StelaVillagomez/funbio-grupo-5/Documentacion/Talleres en clase/Taller 8/Carla Ulloa.pdf

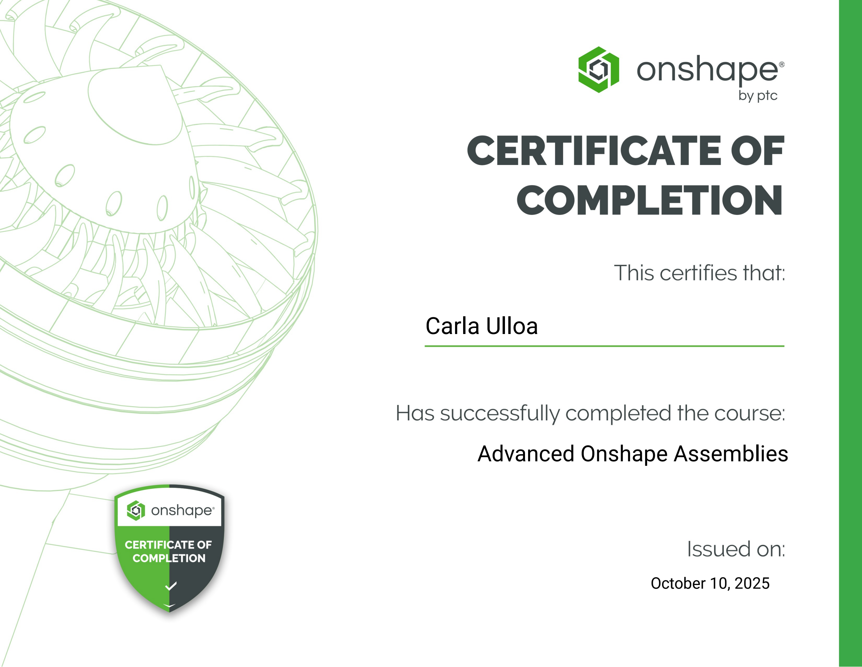
[picture p14: page 1]

Carla Ulloa

Advanced Onshape Assemblies

October 10, 2025
