StelaVillagomez/funbio-grupo-5/Documentacion/Talleres en clase/Taller 8/Luciana Vega.pdf

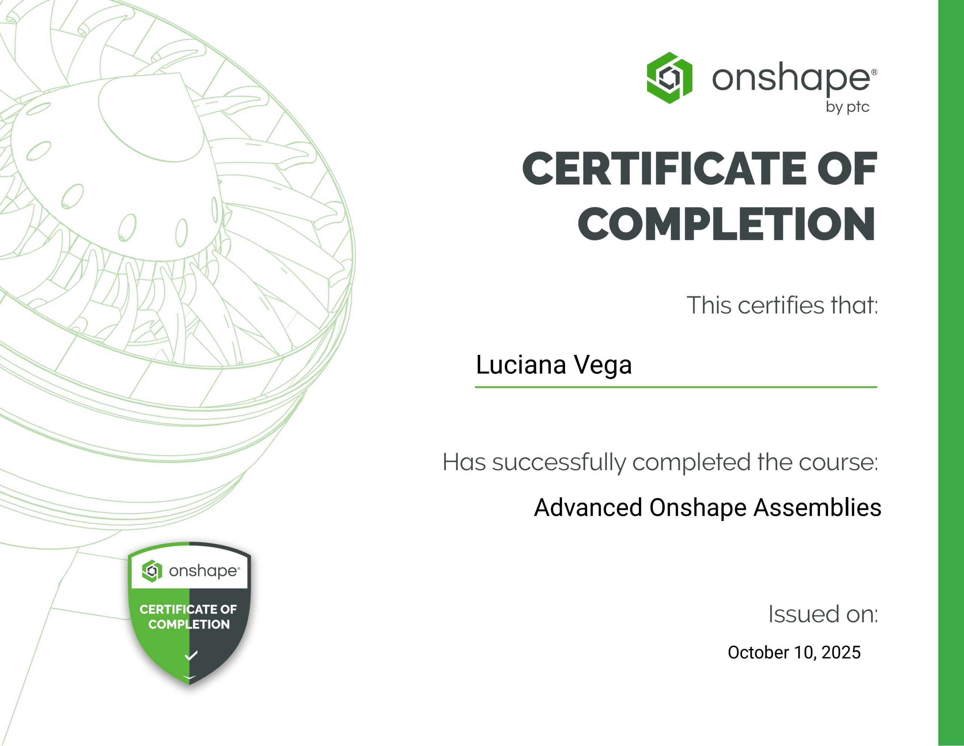
[picture p15: page 1]

Luciana Vega

Advanced Onshape Assemblies

October 10, 2025
