StelaVillagomez/funbio-grupo-5/Documentacion/Talleres en clase/Taller 8/Nahir Valladares.pdf

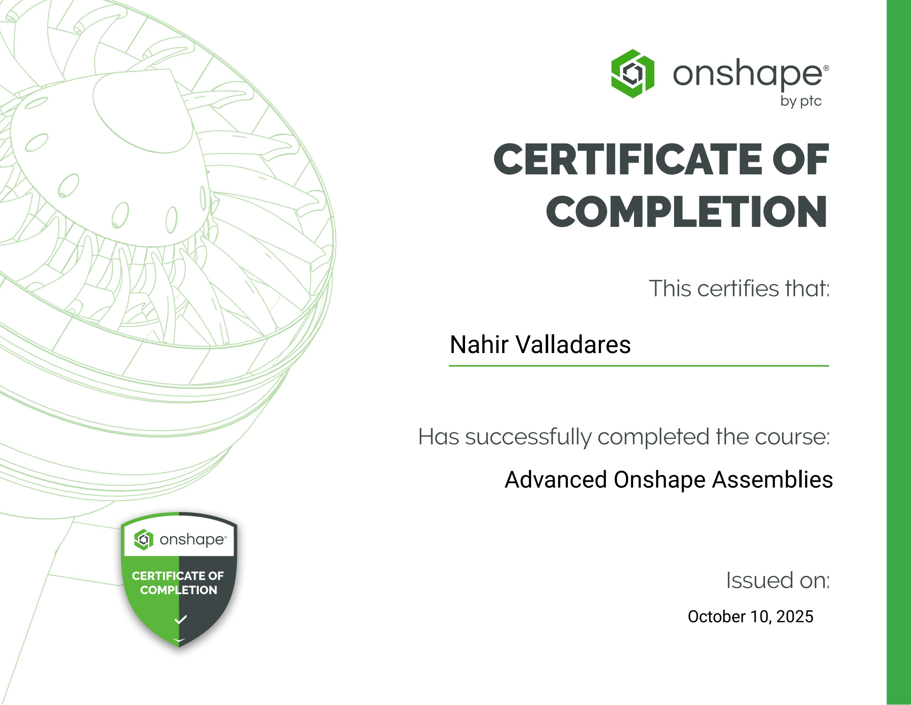
[picture p16: page 1]

Nahir Valladares

Advanced Onshape Assemblies

October 10, 2025
