StelaVillagomez/funbio-grupo-5/Documentacion/Talleres en clase/Taller 8/stela-villagomez.pdf

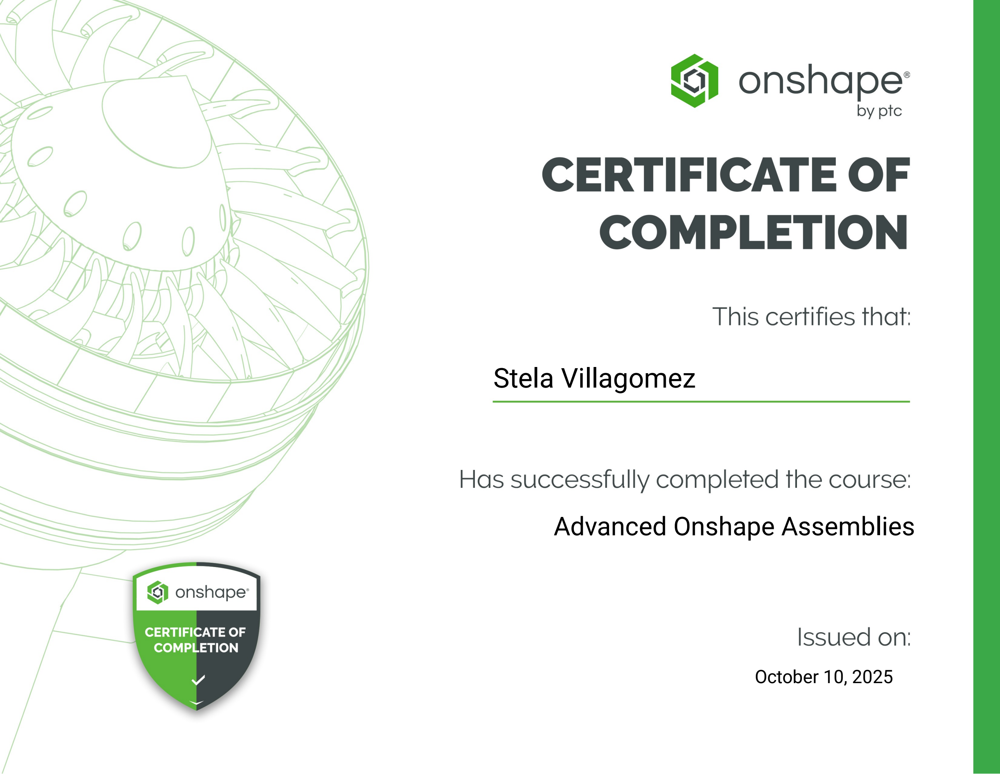
[picture p17: page 1]

Stela Villagomez

Advanced Onshape Assemblies

October 10, 2025
