StelaVillagomez/funbio-grupo-5/Documentacion/Talleres en clase/Taller 8/Carla Victoria.pdf

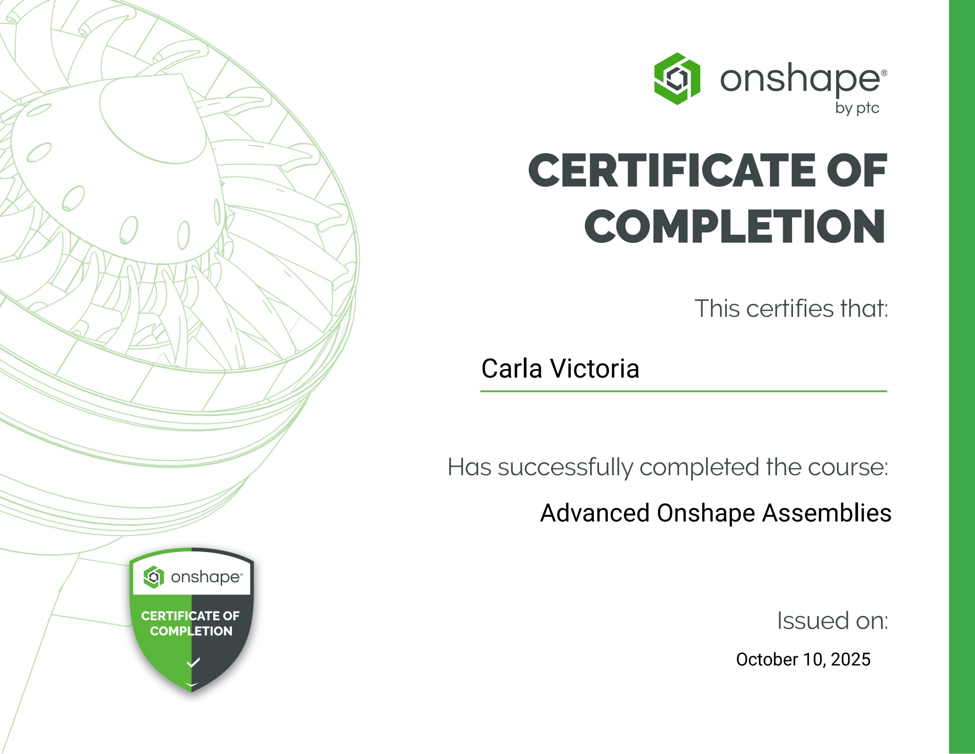
[picture p18: page 1]

Carla Victoria

Advanced Onshape Assemblies

October 10, 2025
