StelaVillagomez/funbio-grupo-5/Documentacion/Talleres en clase/Taller 5 Modelado 3D/Stela Villagomez/stela-villagomez-c9479656-b7c1-46a1-8c88-f6e6d5e3c60f-certificate.pdf

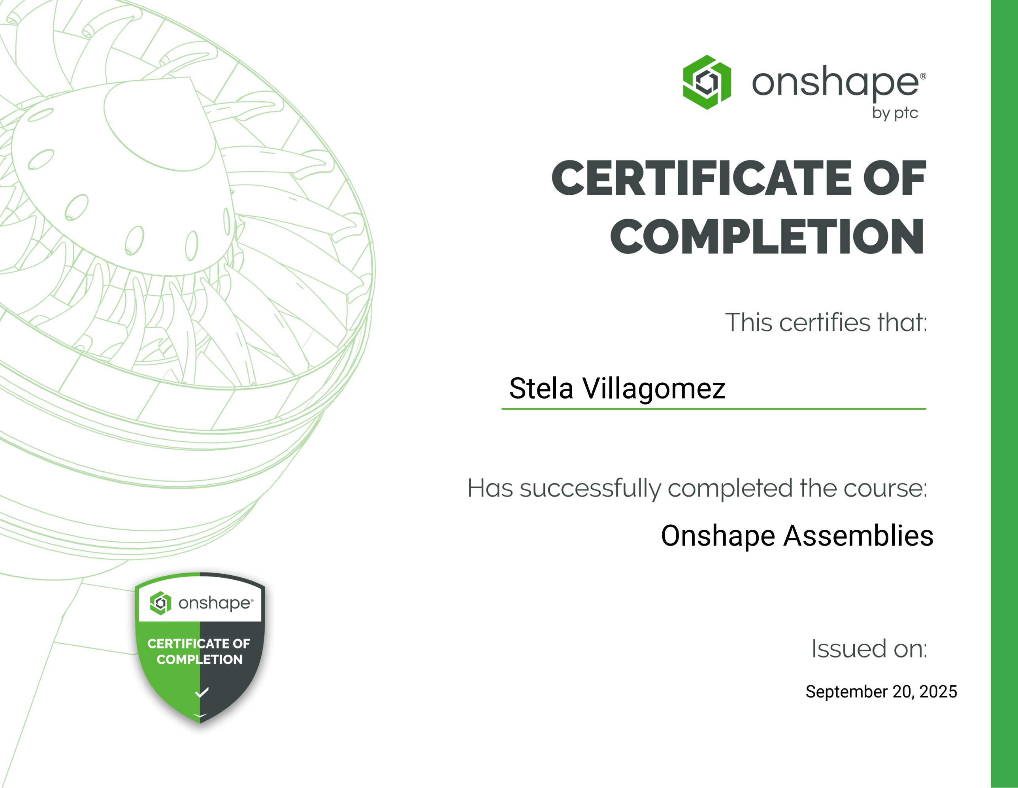
[picture p25: page 1]

Stela Villagomez

September 20, 2025

Onshape Assemblies
