StelaVillagomez/funbio-grupo-5/Documentacion/Talleres en clase/Taller 5 Modelado 3D/Carla Victoria/certificados de los 5 módulos.pdf

Carla Victoria

September 19, 2025

Detailed Drawings

Carla Victoria

Introduction to Part Studios

September 19, 2025

Carla Victoria

Introduction to Sketching

September 17, 2025

Carla Victoria

September 19, 2025

Multi-Part Part Studios

Carla Victoria

September 20, 2025

Onshape Assemblies
