StelaVillagomez/funbio-grupo-5/Documentacion/Entregables/Entregable 9/Entregable 9.pdf

# ENTREGABLE 9

Integrantes:
Carla Ulloa Florián
Nahir Valladares Santur
Luciana Vega Llanos
Carla Victoria Quispe
Stela Villagomez Altamirano Almendra Yataco Diaz

Profesor:
Juan Manuel Zuñiga

Curso:
Fundamentos de Biodiseño

2025


Hardware Electronico

Diseño esquemático del circuito electrónico:

Link:
https://u.easyeda.com/join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 (https://u.easyeda.com/join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)

Componentes físicos implementados más código:

Software (si tenemos, sino borrar)




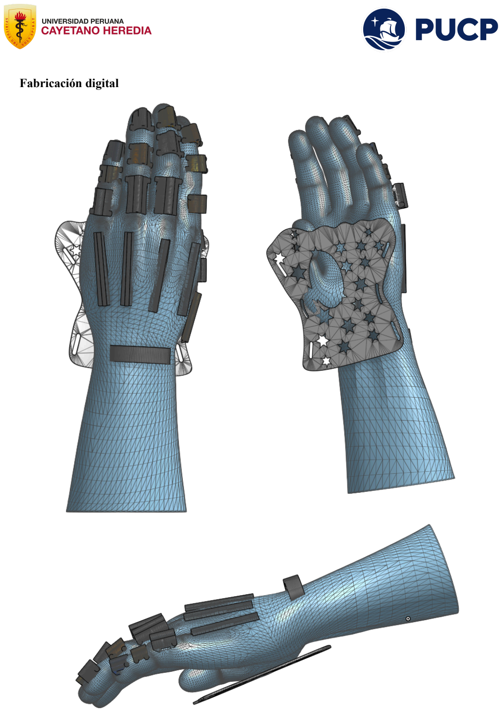
[picture p60: page 7]

Fabricación digital

Plan de usabilidad basado en evidencias Sección del
plan
¿Qué es? | ¿Qué hacer? | ¿Qué evidencia deben
incluir?

Contexto de
uso

Describe el entorno
físico, social y técnico
donde el usuario emplea
el | guante | de
rehabilitación
MasiHand
El | usuario | es | un
paciente con hemiplejía
post-ACV hemorrágico
con mano en flexión.
dispositivo | es | una
persona que ha sufrido
de ACV y
El | dispositivo | está
creado | para | ser
utilizado,
principalmente, en el
hogar del paciente. Para
ello, requiere de una
mesa/superficie plana,
segura y estable. El
paciente | será
previamente instruido
por su terapeuta sobre el
uso del dispositivo en
una | sesión
introductoria. Donde le
explicará | el
funcionamiento | del
sistema, | el | cual,
consiste, en que el
paciente | vía | una
aplicación móvil que
descargará en su celular
podrá inicializar su
movimiento | de
extensión | para | una
sesión de rehabilitación
de 30 minutos.
A | continuación | se
adjunta foto de la
colocación | del
dispositivo | en | un
modelado 3D

Perfil del
usuario

Caracteriza al usuario
final del sistema, sus
limitaciones,
capacidades | y
motivaciones

Mujer de 55 años con
hemiplejía | derecha
espástica | (Ashworth
2–3), leve disartria, y
uso dominante de la
mano izquierda. Vive

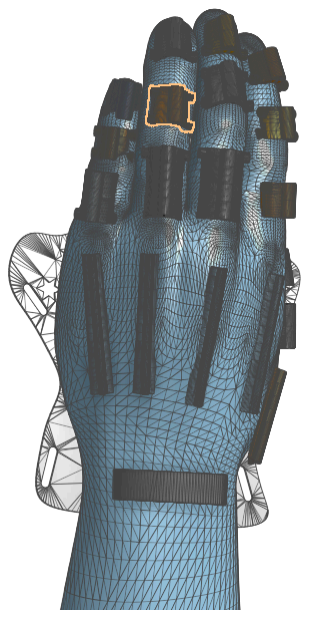
[picture p61: figure]

Evidencia basada en el
caso clínico presentado
a nosotros.

Ficha resumen del caso
clínico:

con su esposo e hija,
muestra alta motivación
por | recuperar
autonomía | | en
actividades | como
vestirse, | cocinar | y
escribir, | aunque
presenta frustración al
no poder usar su mano
derecha.

Paciente: Mujer, 55
años
Diagnóstico:
Hemiplejía | derecha
espástica | post-ACV
hemorrágico
Antecedentes:
Hipertensión arterial
mal controlada
Estado | actual:
Espasticidad moderada
(Ashworth 2–3), mano
derecha | en | flexión
permanente, | leve
disartria, marcha con
bastón.
Dolor: | Tirantez | y
rigidez al extender la
mano.
Situación social: Vive
con esposo e hija; ex
costurera, ahora realiza
tareas ligeras.
Tratamientos previos:
Fisioterapia, | férula
nocturna, | baclofeno,
toxina botulínica.
Meta: Recuperar
autonomía en AVD y
funcionalidad de la
mano.

Análisis de
tareas

Identifica las acciones
que el usuario realiza o
debe aprender para
interactuar
correctamente con el
sistema
1. El paciente fue
previamente
instruido por su
terapeuta
2. Colocar férula
para la extensión
de su muñeca
3. Colocación del
guante
4. Presionar | el
botón | de

El paciente conforme
vaya | | realizando
progresivamente | el
tratamiento debe poseer
la capacidad de realizar
una extensión , la
evidencia se basa en el
uso | del | dispositivo
como tal.

encendido
5. Registrar
movimiento
máximo del
paciente por si
mismo
6. Inicializar el
movimiento
predeterminado
durante 30
minutos
7. El | tiempo
terminado,
apagar el equipo
8. Retirar el guante
y luego la férula

Criterios de
éxito

Define las métricas que
permiten evaluar la
efectividad y usabilidad
del dispositivo
- Satisfacción: El
paciente se siente
cómodo,
motivado y
seguro al usar el
guante.
- Seguridad: | no
presenta | dolor,
lesiones | ni
movimientos
bruscos durante
el uso.
- Adherencia: la
paciente
mantiene el uso
regular | del
dispositivo | en
casa.
El | paciente | dará
feedback de su uso del
guante mecánico. Se
calificará en una escala
del 1 al 10 cada sección
y se tendrán en cuenta
comentarios para
mejorar a futuro.
