StelaVillagomez/funbio-grupo-5/Documentacion/Talleres en clase/Taller 8/Almendra Yataco.pdf

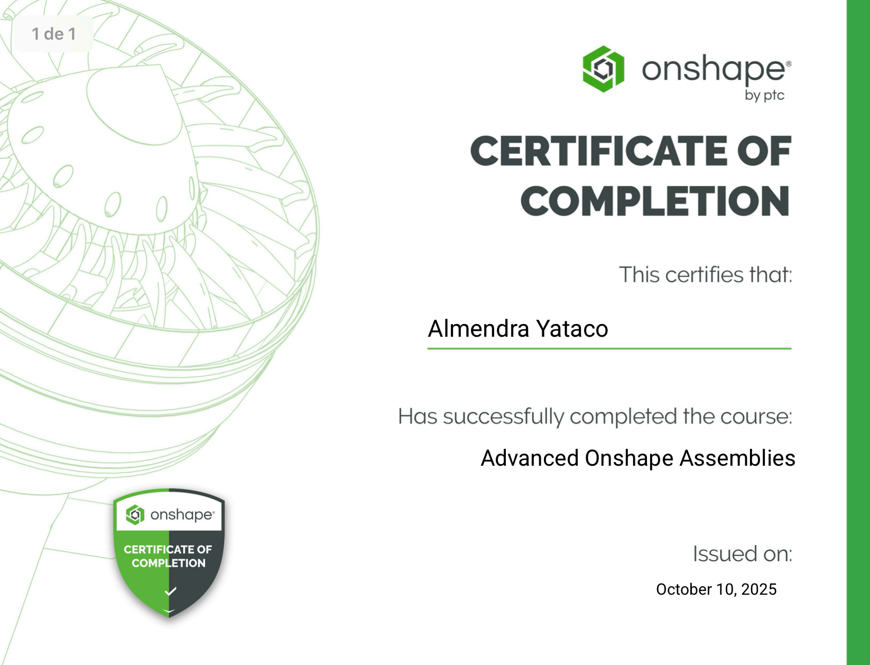
[picture p62: figure]
