StelaVillagomez/funbio-grupo-5/Documentacion/Talleres en clase/Taller 5 Modelado 3D/Luciana Vega/lucianavega_certificado_Detailed Drawings.pdf

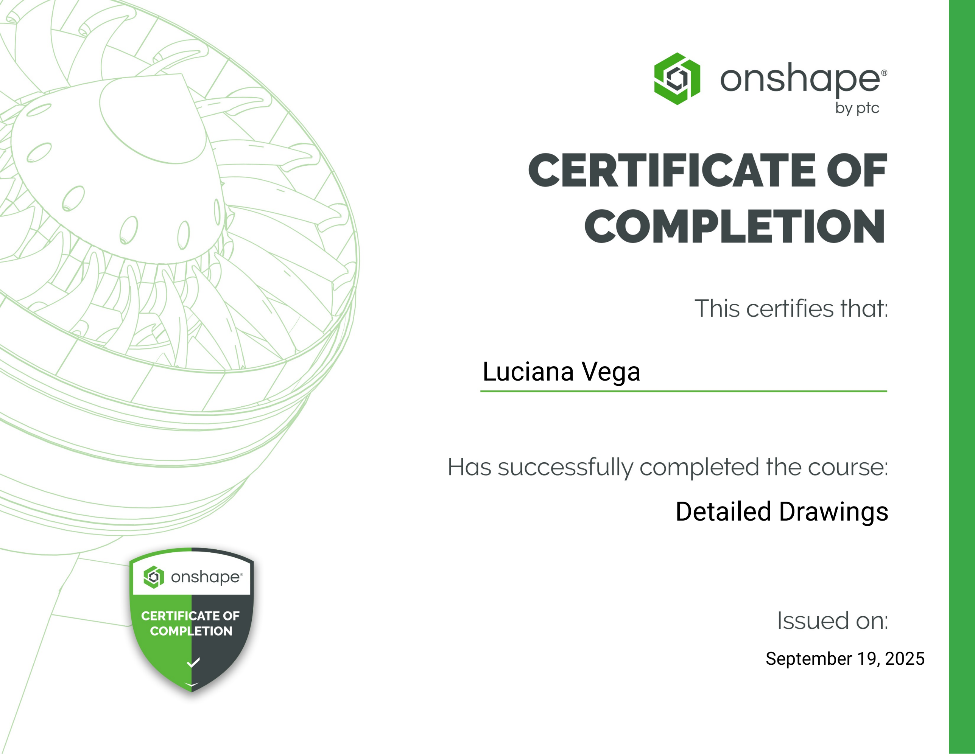
[picture p63: page 1]

Luciana Vega

September 19, 2025

Detailed Drawings
