StelaVillagomez/funbio-grupo-5/Documentacion/Talleres en clase/Taller 5 Modelado 3D/Luciana Vega/lucianavega_certificado_Introduction to Part Studio.pdf

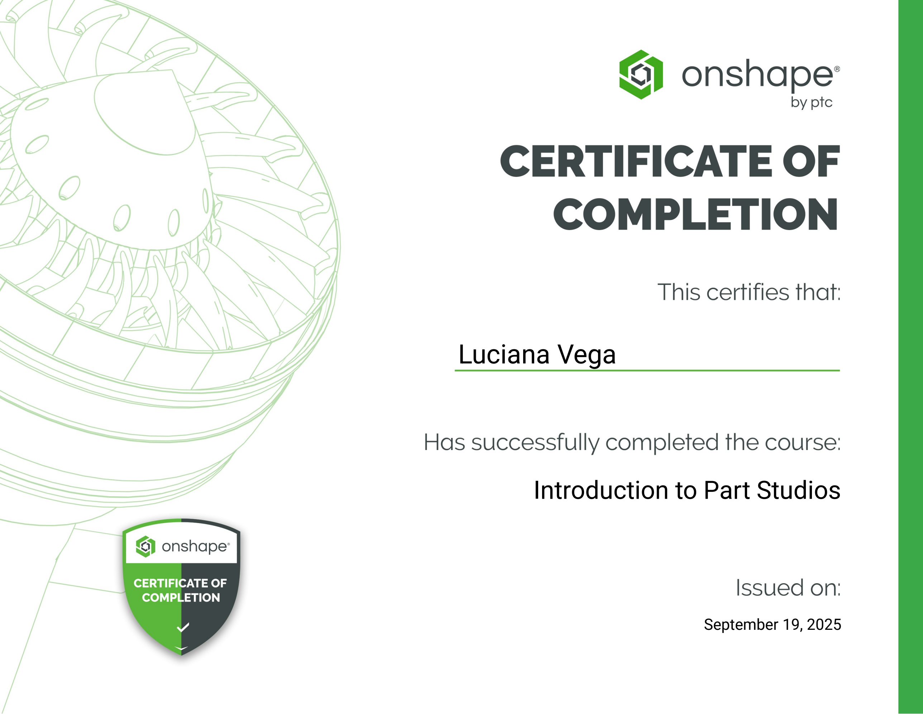
[picture p64: page 1]

Luciana Vega

Introduction to Part Studios

September 19, 2025
