StelaVillagomez/funbio-grupo-5/Documentacion/Talleres en clase/Taller 5 Modelado 3D/Luciana Vega/lucianavega_certificado_Introduction to Sketching.pdf

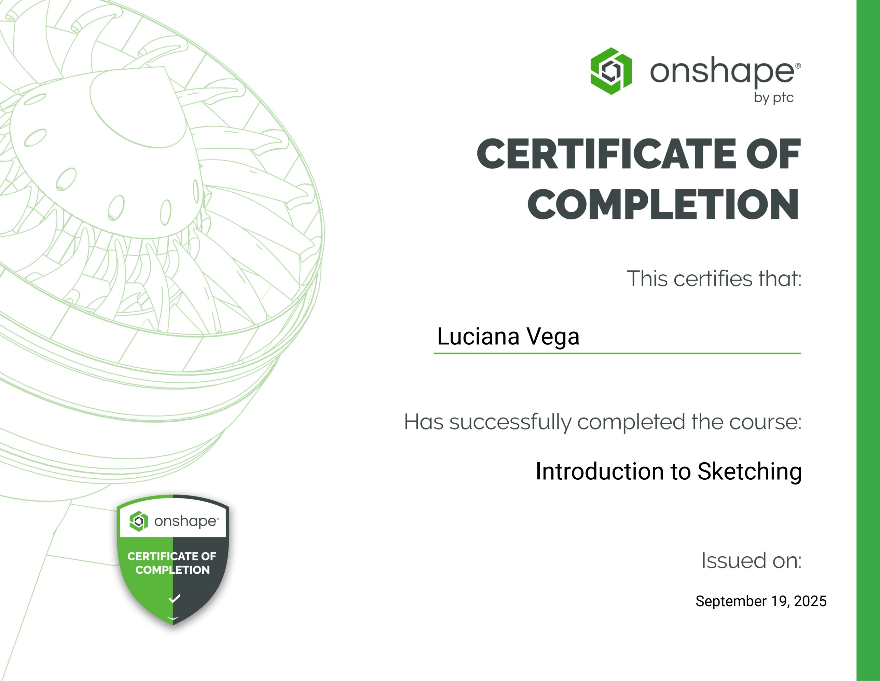
[picture p65: page 1]

Luciana Vega

Introduction to Sketching

September 19, 2025
