StelaVillagomez/funbio-grupo-5/Documentacion/Talleres en clase/Taller 5 Modelado 3D/Luciana Vega/lucianavega_certificado_Multi-part Part Studios.pdf

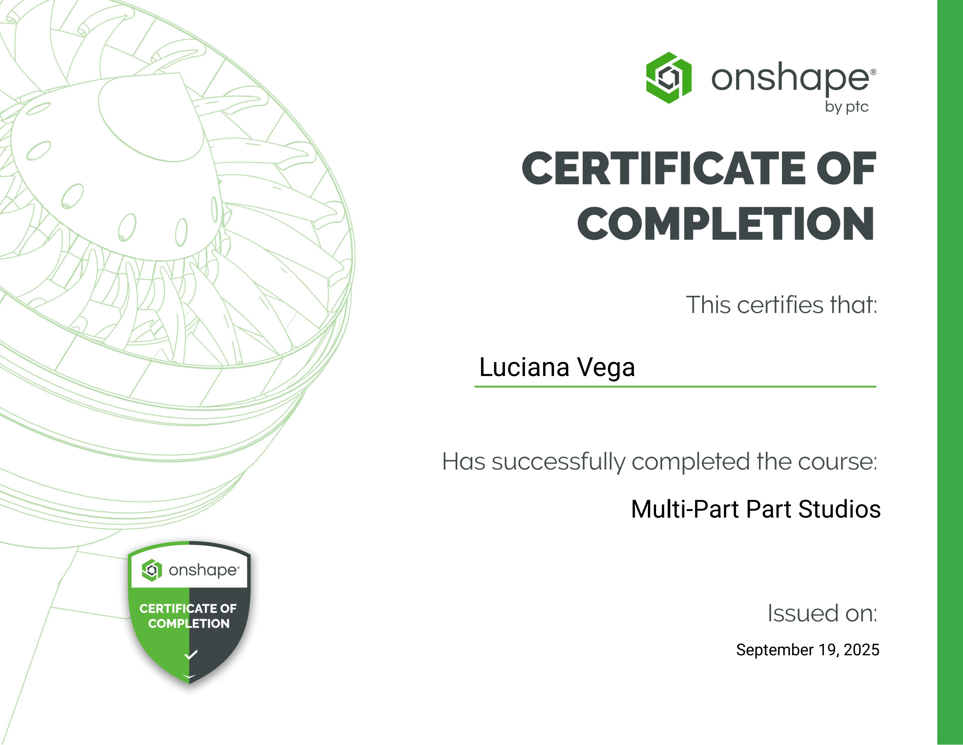
[picture p66: page 1]

Luciana Vega

September 19, 2025

Multi-Part Part Studios
