StelaVillagomez/funbio-grupo-5/Documentacion/Talleres en clase/Taller 5 Modelado 3D/Stela Villagomez/stela-villagomez-3291569b-ad46-43eb-bca6-9398602f4097-certificate.pdf

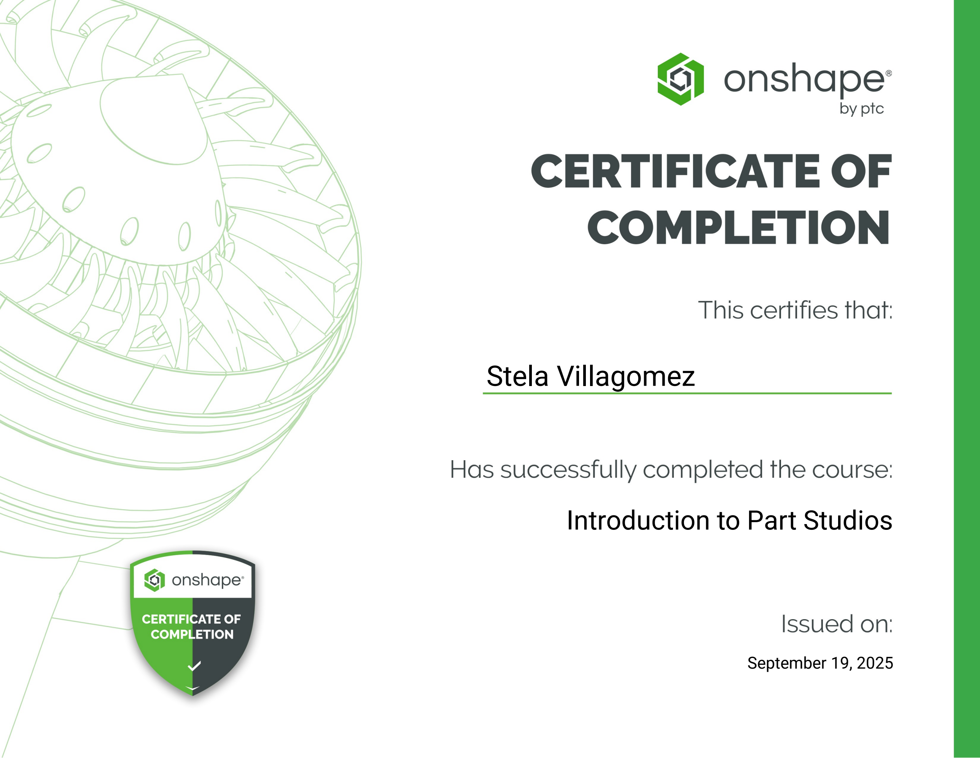
[picture p67: page 1]

Stela Villagomez

Introduction to Part Studios

September 19, 2025
