StelaVillagomez/funbio-grupo-5/Documentacion/Talleres en clase/Taller 5 Modelado 3D/Stela Villagomez/stela-villagomez-7ee65e5e-5e09-4878-9e36-502a13041336-certificate.pdf

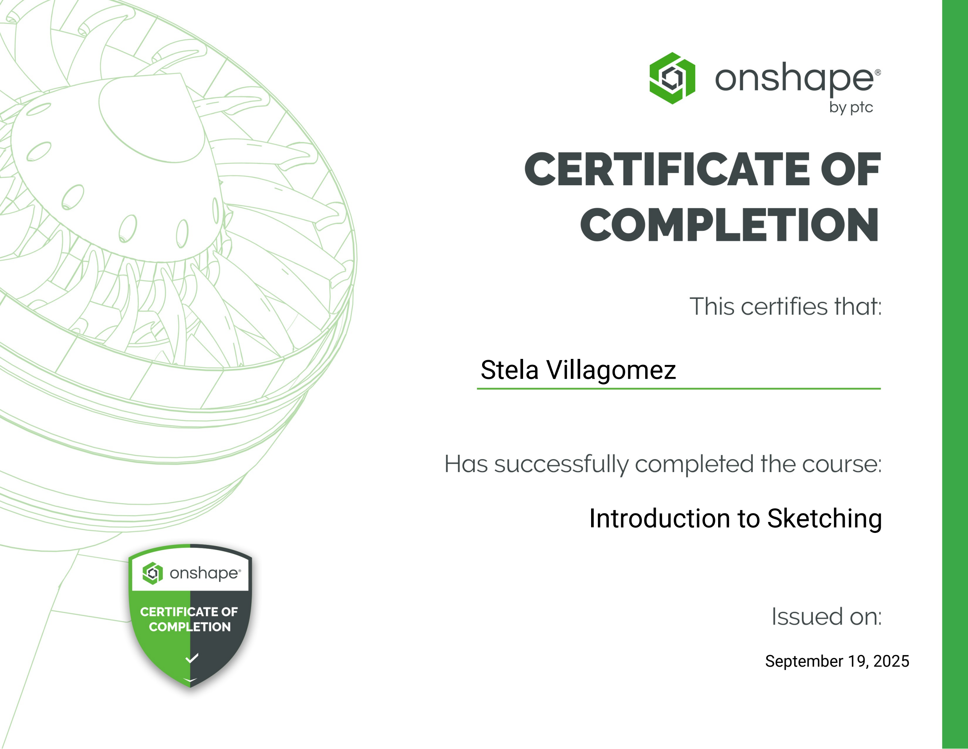
[picture p68: page 1]

Stela Villagomez

Introduction to Sketching

September 19, 2025
