StelaVillagomez/funbio-grupo-5/Documentacion/Talleres en clase/Taller 5 Modelado 3D/Stela Villagomez/stela-villagomez-90a80670-adc8-4174-b212-e4f41012d839-certificate.pdf

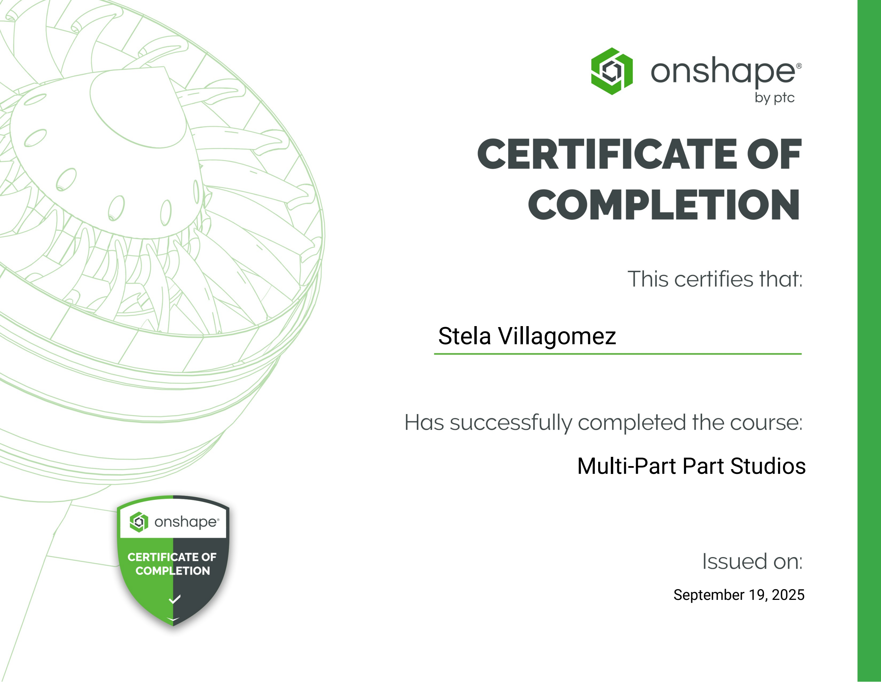
[picture p69: page 1]

Stela Villagomez

September 19, 2025

Multi-Part Part Studios
