StelaVillagomez/funbio-grupo-5/Documentacion/Talleres en clase/Taller 5 Modelado 3D/Stela Villagomez/stela-villagomez-a9cecc1e-69a0-46b0-b9f3-93bf0a22dbf1-certificate.pdf

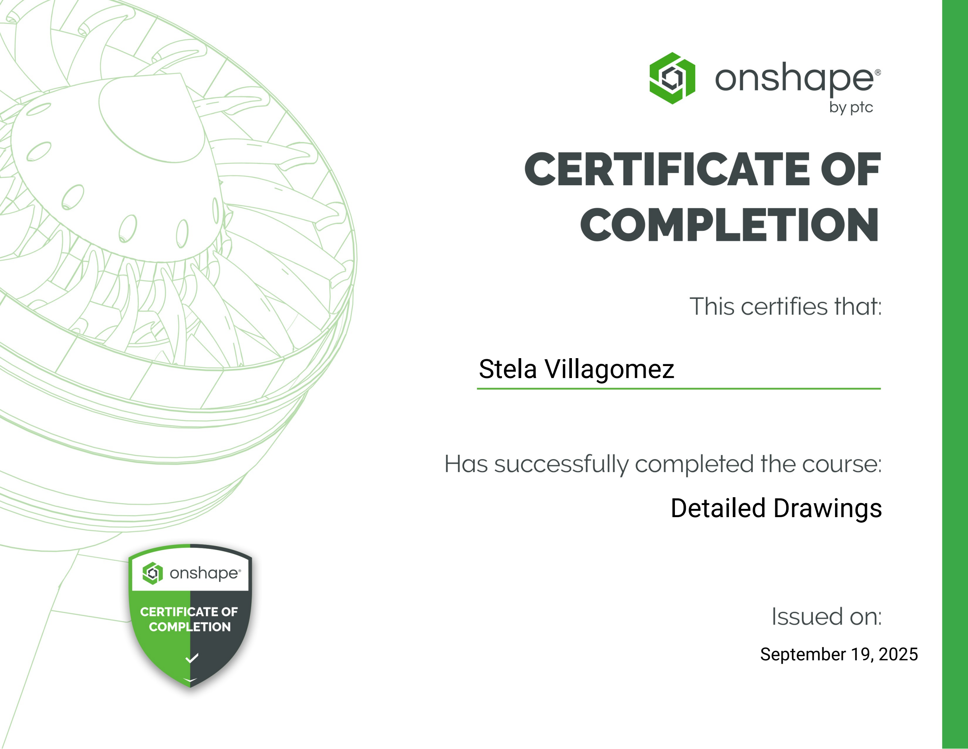
[picture p70: page 1]

Stela Villagomez

September 19, 2025

Detailed Drawings
