StelaVillagomez/funbio-grupo-5/Documentacion/Talleres en clase/Taller 5 Modelado 3D/Nahir Valladares/Ejercicios de evidencia.pdf

Algunos ejercicios de evidencia

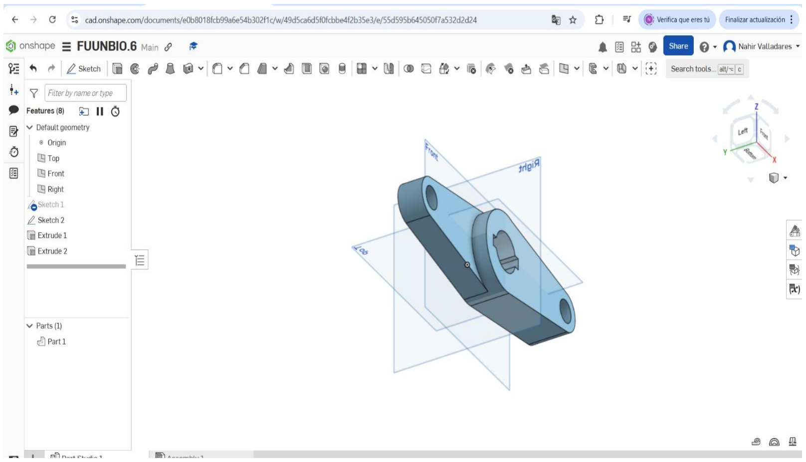
[picture p71: figure]
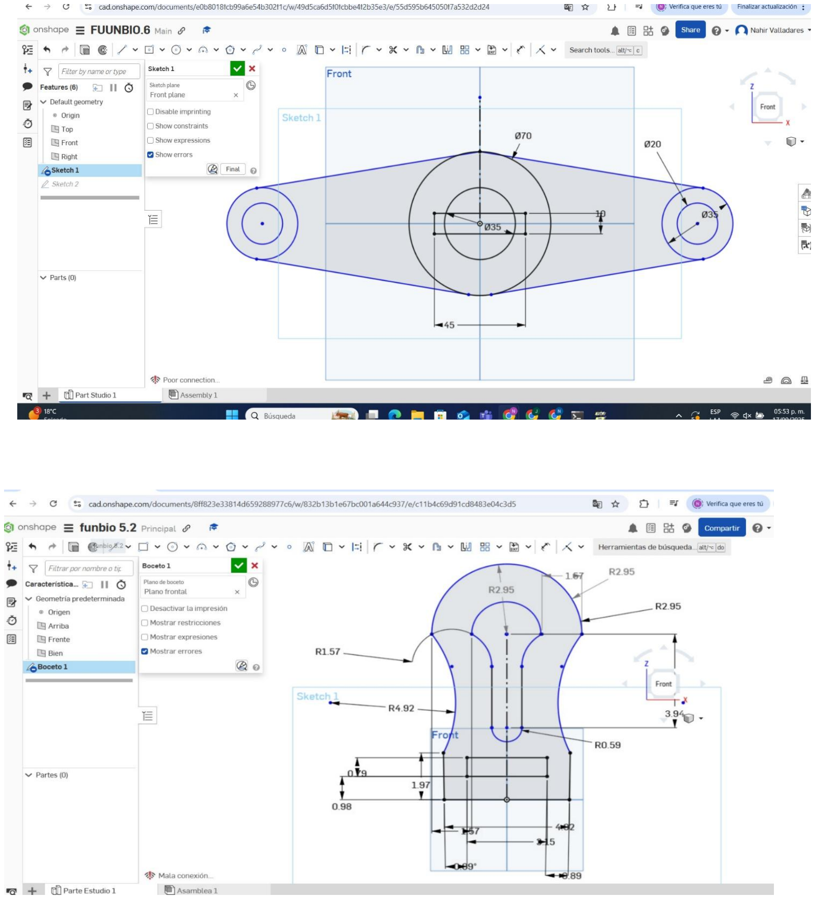
[picture p72: page 2]
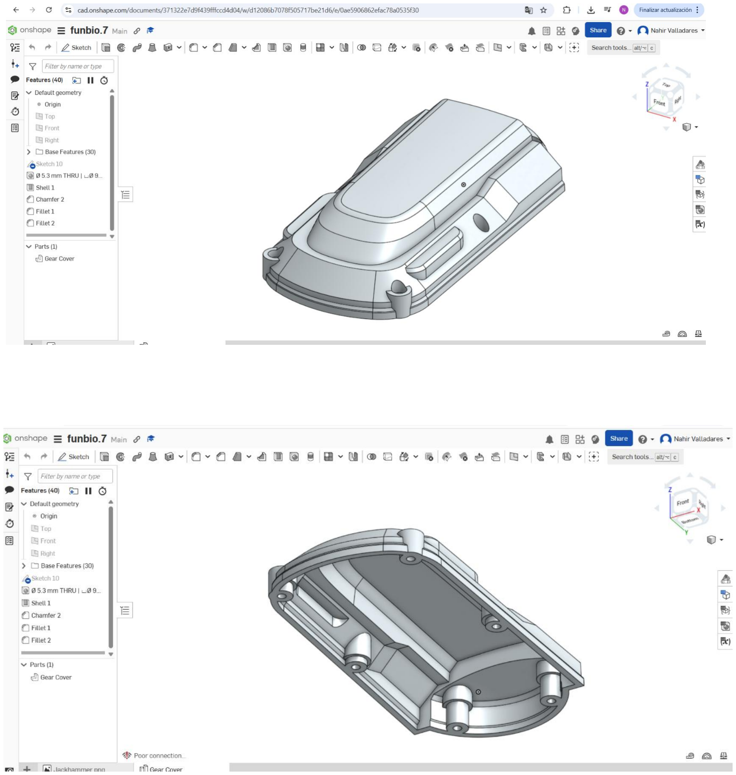
[picture p73: page 3]
