StelaVillagomez/funbio-grupo-5/Documentacion/Talleres en clase/Taller 5 Modelado 3D/Almendra Yataco/Taller 5 - Almendra Yataco.pdf

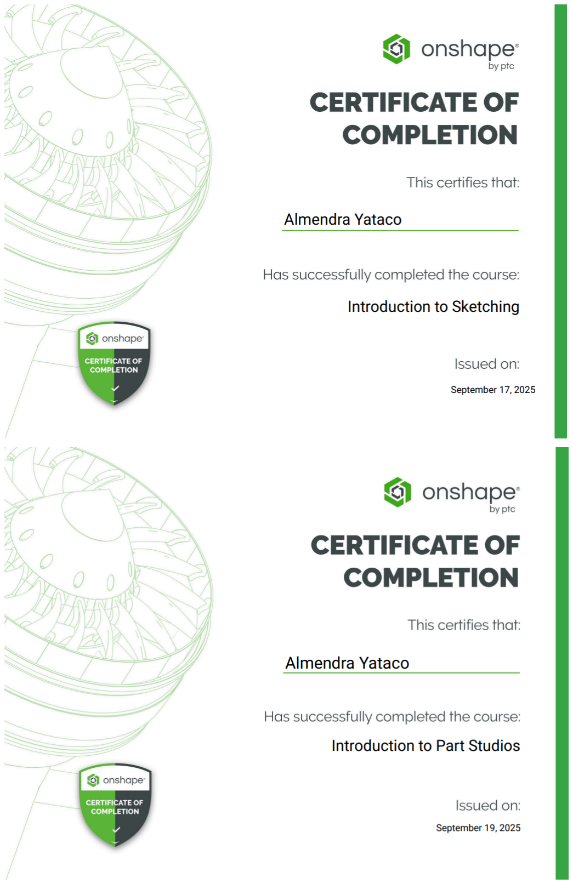
[picture p74: page 1]
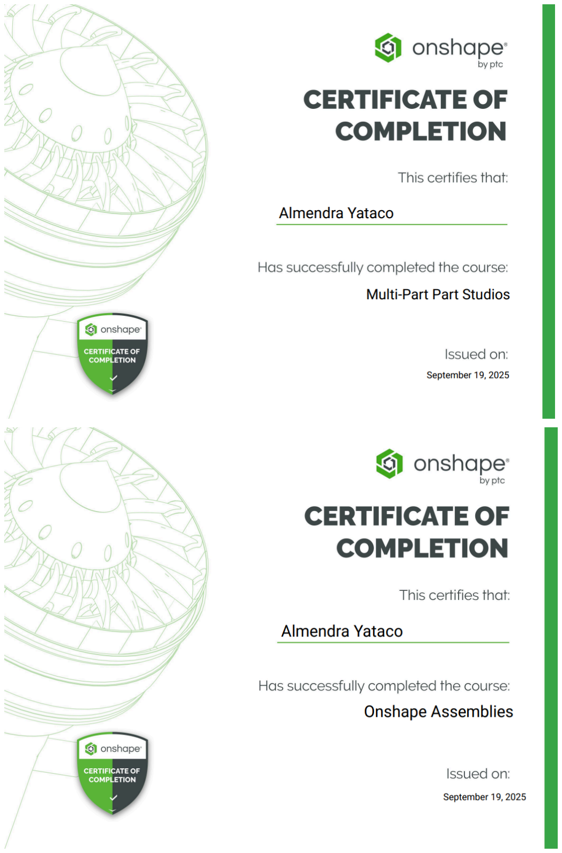
[picture p75: page 2]

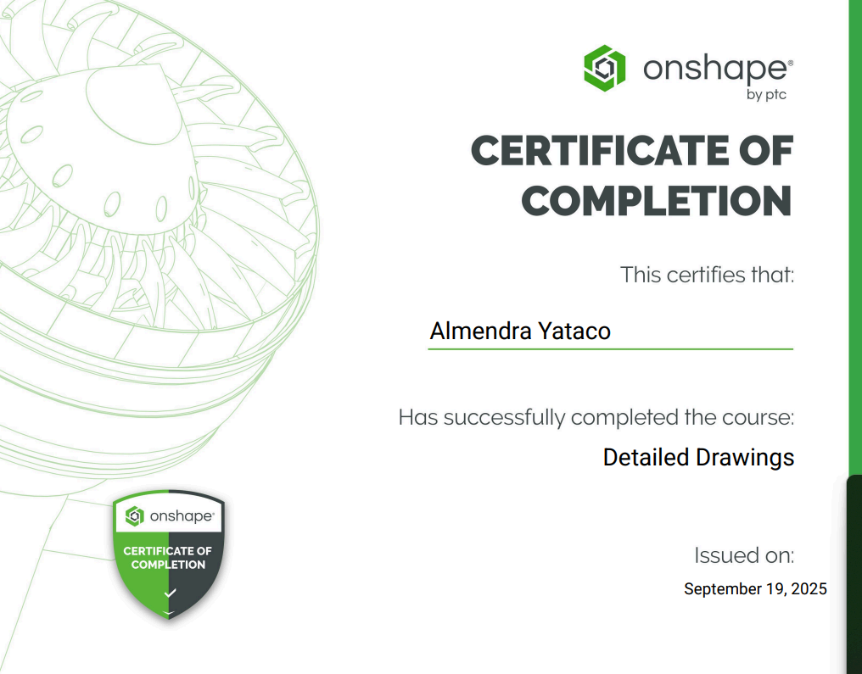
[picture p76: figure]
