StelaVillagomez/funbio-grupo-5/Documentacion/Talleres en clase/Taller 5 Modelado 3D/Nahir Valladares/certificado deleite drawing.pdf

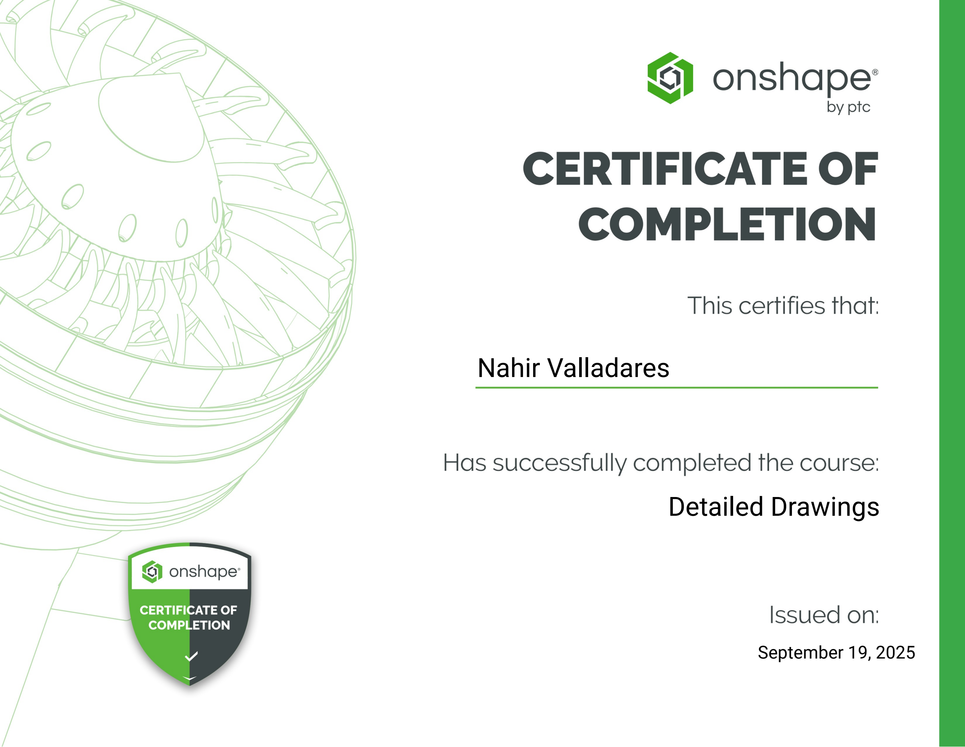
[picture p77: page 1]

Nahir Valladares

September 19, 2025

Detailed Drawings
