StelaVillagomez/funbio-grupo-5/Documentacion/Talleres en clase/Taller 5 Modelado 3D/Nahir Valladares/certificado introduction to part studios.pdf

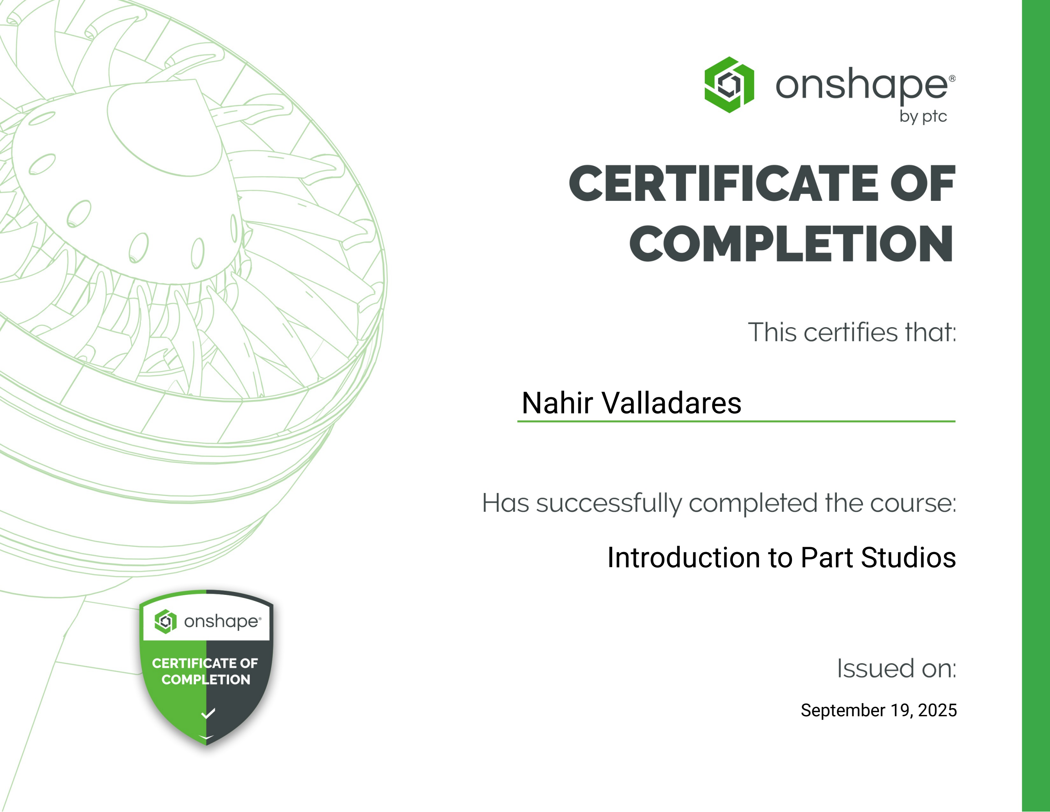
[picture p78: page 1]

Nahir Valladares

Introduction to Part Studios

September 19, 2025
