StelaVillagomez/funbio-grupo-5/Documentacion/Talleres en clase/Taller 5 Modelado 3D/Nahir Valladares/certificado introduction to sketching.pdf

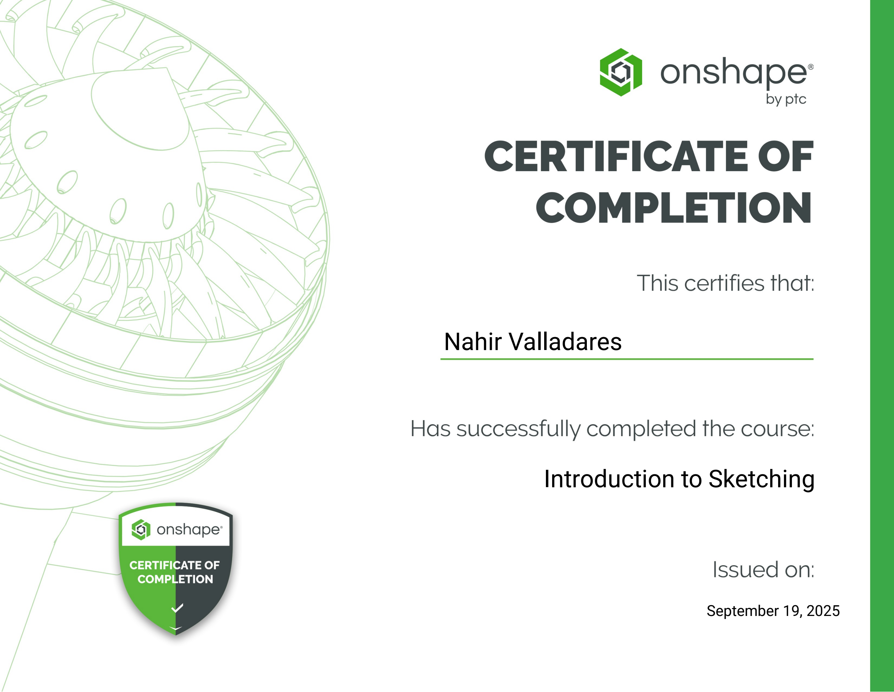
[picture p79: page 1]

Nahir Valladares

Introduction to Sketching

September 19, 2025
