StelaVillagomez/funbio-grupo-5/Documentacion/Talleres en clase/Taller 5 Modelado 3D/Nahir Valladares/certificado multipart part studios.pdf

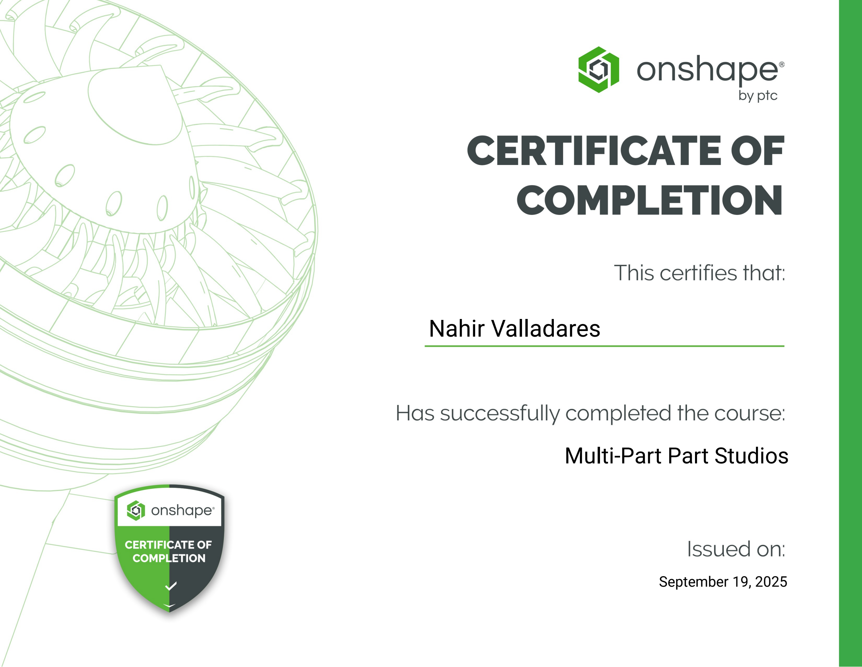
[picture p80: page 1]

Nahir Valladares

September 19, 2025

Multi-Part Part Studios
