StelaVillagomez/funbio-grupo-5/Documentacion/Entregables/Entregable 9/Foto del modelado 2.jpeg

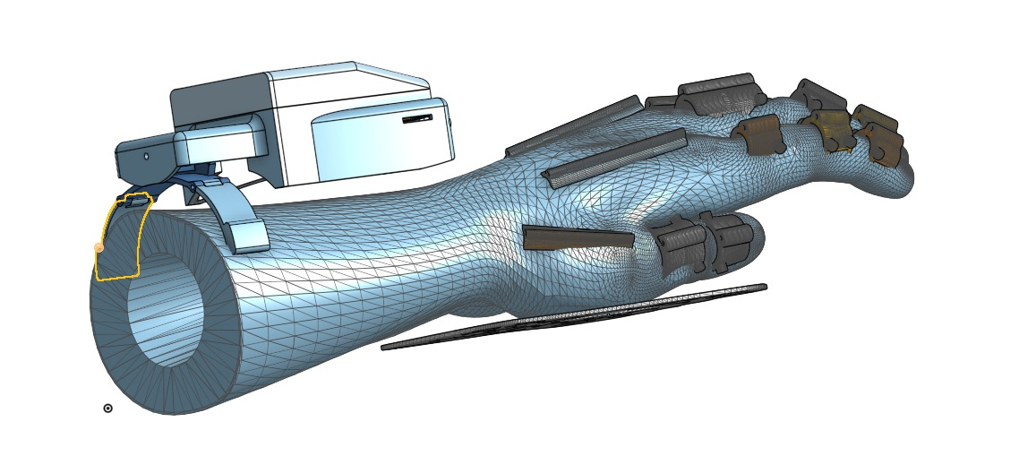
Documentacion/Entregables/Entregable 9/Foto del modelado 2.jpeg
