StelaVillagomez/funbio-grupo-5/Documentacion/Talleres en clase/Taller 6 - Actuadores/Actividad 2/Código 2.jpeg

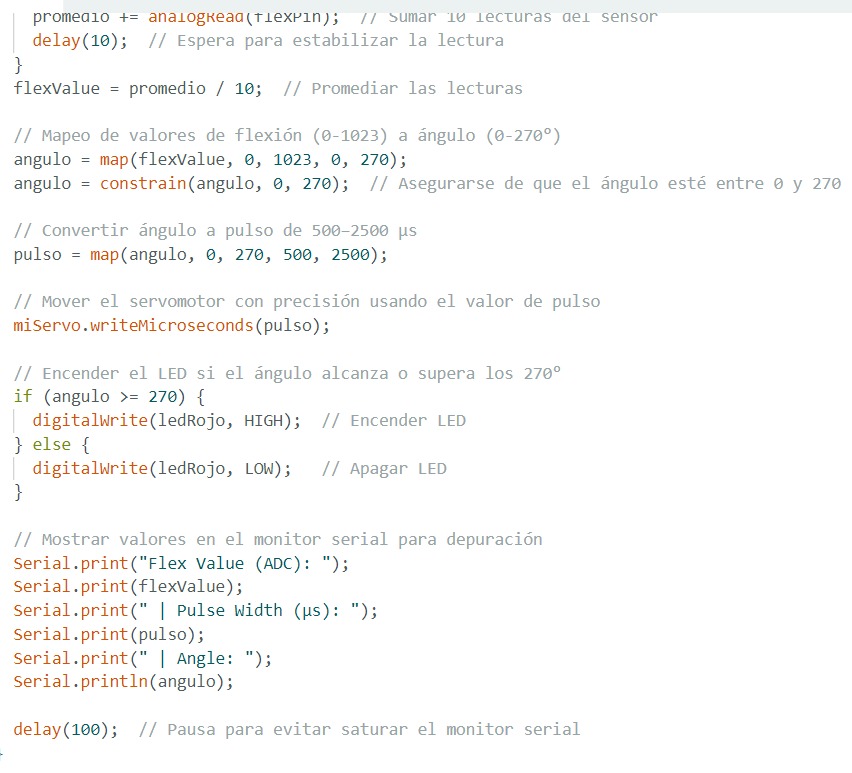
Documentacion/Talleres en clase/Taller 6 - Actuadores/Actividad 2/Código 2.jpeg
