StelaVillagomez/funbio-grupo-5/Documentacion/Talleres en clase/Taller de sensores/Actividad 1/Código.jpeg

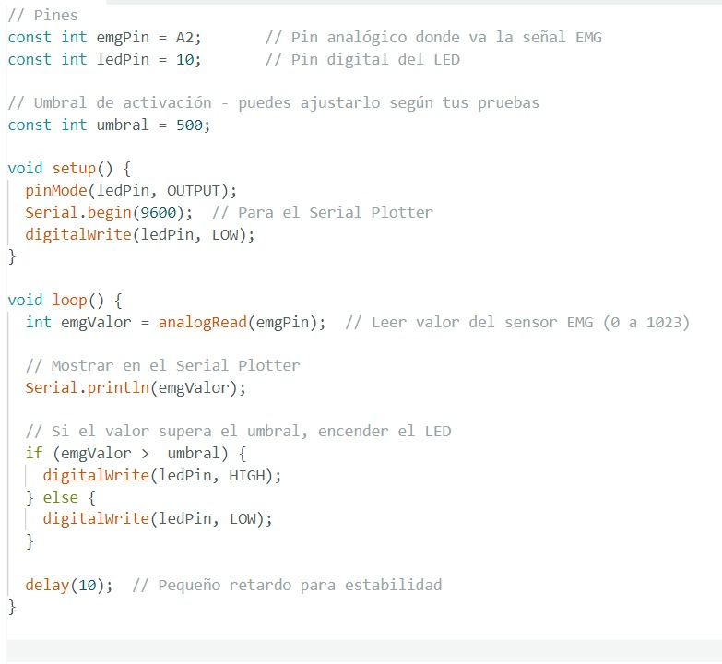
Documentacion/Talleres en clase/Taller de sensores/Actividad 1/Código.jpeg
