StelaVillagomez/funbio-grupo-5/Documentacion/Talleres en clase/Taller de sensores/Actividad 1/valores en tenso.jpeg

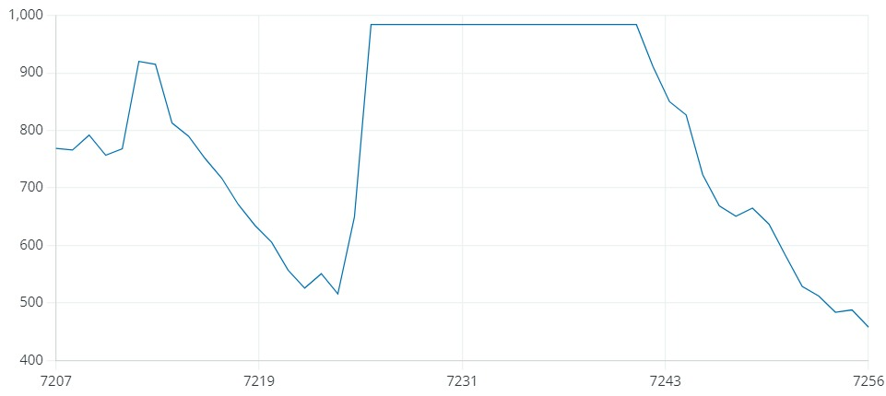
Documentacion/Talleres en clase/Taller de sensores/Actividad 1/valores en tenso.jpeg
