StelaVillagomez/funbio-grupo-5/Documentacion/Talleres en clase/Taller de sensores/Actividad 1/Valores relajado.jpeg

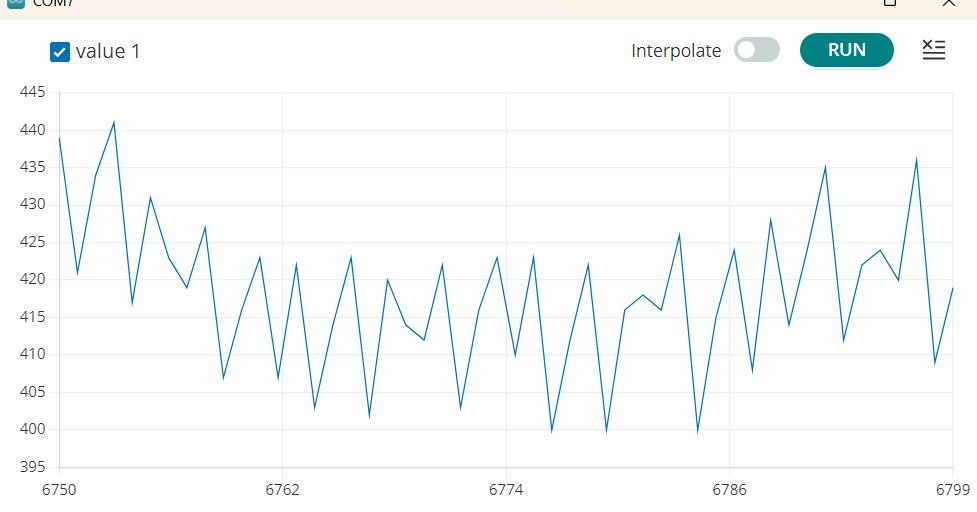
Documentacion/Talleres en clase/Taller de sensores/Actividad 1/Valores relajado.jpeg
