StelaVillagomez/funbio-grupo-5/Documentacion/Talleres en clase/Taller de sensores/Actividad 2/Codigo parte II.jpeg

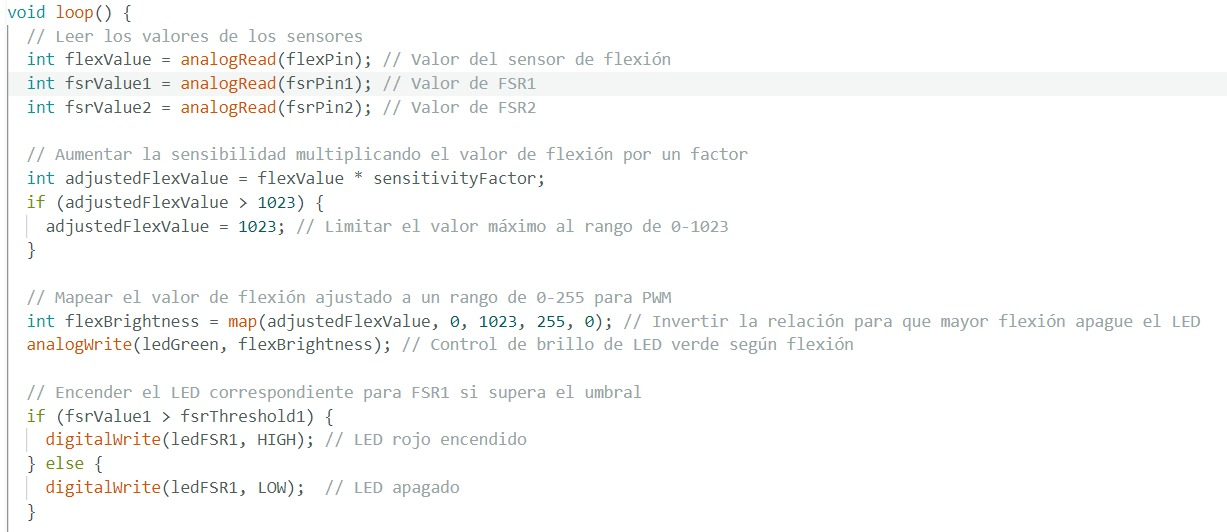
Documentacion/Talleres en clase/Taller de sensores/Actividad 2/Codigo parte II.jpeg
