StelaVillagomez/funbio-grupo-5/Documentacion/Talleres en clase/Taller de sensores/Actividad 3/Código parte I.jpeg

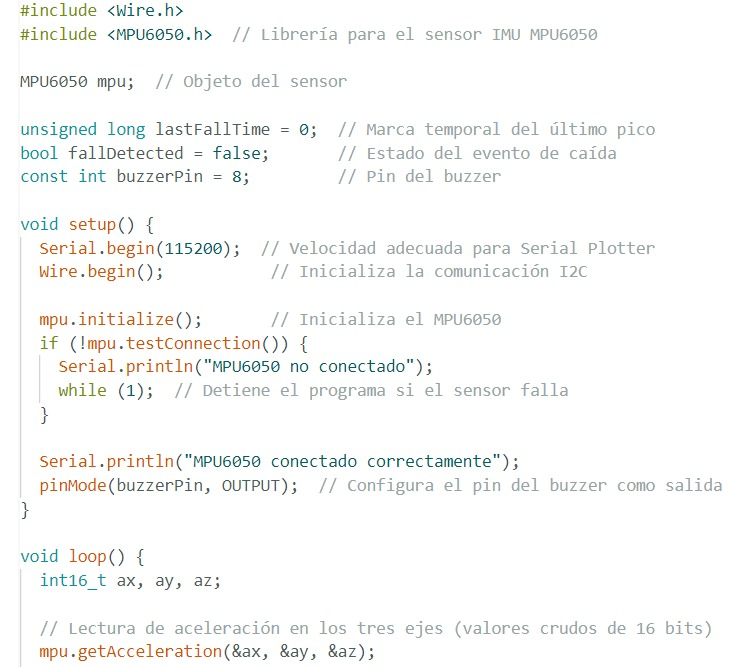
Documentacion/Talleres en clase/Taller de sensores/Actividad 3/Código parte I.jpeg
