StelaVillagomez/funbio-grupo-5/Documentacion/Talleres en clase/Taller de sensores/Actividad 3/Código parte II.jpeg

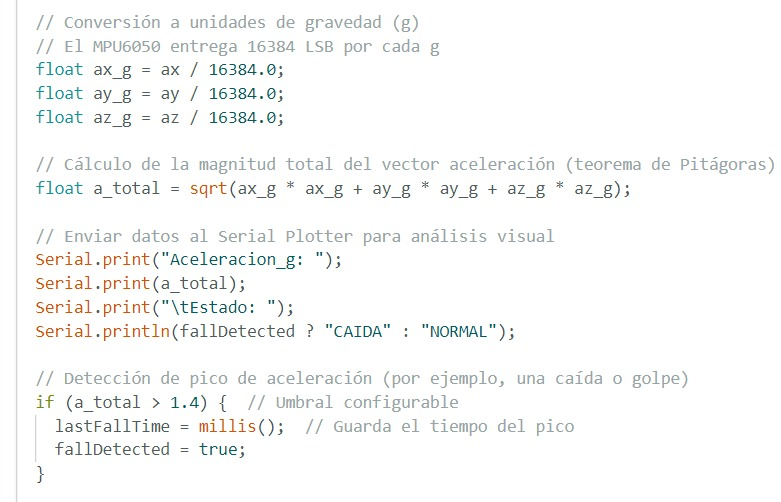
Documentacion/Talleres en clase/Taller de sensores/Actividad 3/Código parte II.jpeg
