StelaVillagomez/funbio-grupo-5/Documentacion/Entregables/Entregable 9/Exoesqueleto +férula stl/Dedo índice/Índice 1.stl

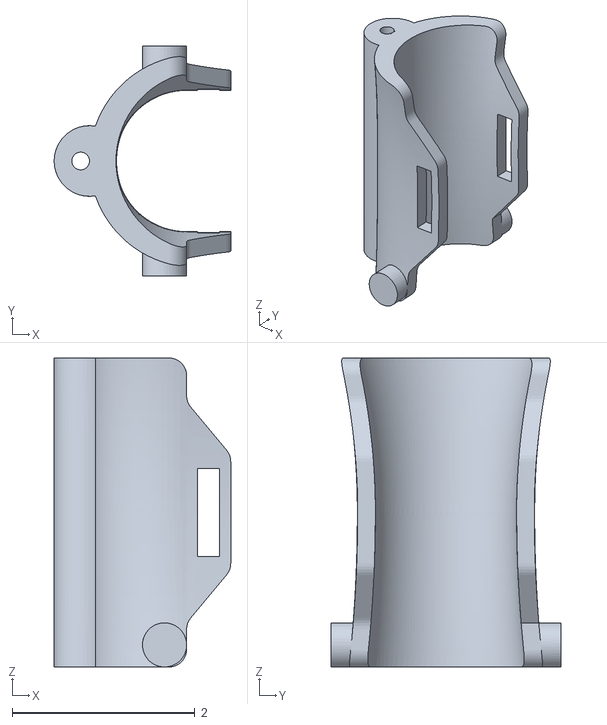
[picture p116: CAD file, 2025-10-29]
Documentacion/Entregables/Entregable 9/Exoesqueleto +férula stl/Dedo índice/Índice 1.stl
1.93 x 2.51 x 3.38
