StelaVillagomez/funbio-grupo-5/Documentacion/Talleres en clase/Taller 6 - Actuadores/Actividad 1/Circuito armado.jpeg

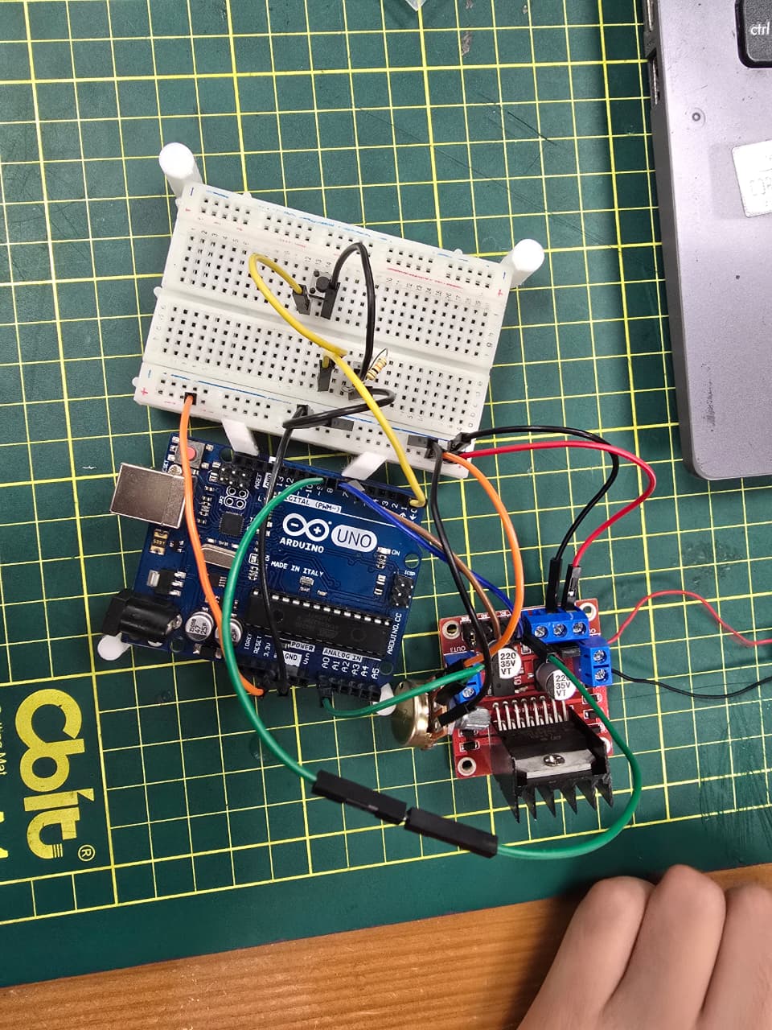
Documentacion/Talleres en clase/Taller 6 - Actuadores/Actividad 1/Circuito armado.jpeg
